Seeed-Studio/OSHW-XIAO-Debug-Mate/1_Libraries/Seeed_Arduino_DAPLink/README.md

# Seeed_Arduino_DAPLink

Most of Seeed & Adafruit boards Seeeduino M0/M4, featuring M0, M4 and nRF52840 are able to run the daplink sketch. It allows us to flash/burn bootloader of any ARM Cortex-M MCU (M0, M4, nRF52832, nRF52840 etc ..) and step debugging with gdb and/or supported IDE such as eclipse,  Keil, IAR. For your convenience, a precompiled daplink firmware in uf2 format for specific board can be found at wiki page

[**More detailed documentation**](https://wiki.seeedstudio.com/Arduino-DAPLink/)

## Contributing
Contributing to this software is warmly welcomed. You can do this basically by<br>
[forking](https://help.github.com/articles/fork-a-repo), committing modifications and then [pulling requests](https://help.github.com/articles/using-pull-requests) (follow the links above<br>
for operating guide). Adding change log and your contact into file header is encouraged.<br>
Thanks for your contribution.
