Seeed-Studio/OSHW-XIAO-Debug-Mate/1_Libraries/lvgl_debug_mate/tests/ref_imgs/draw/render/al88/demo_render_image_recolor_1_opa_128.png

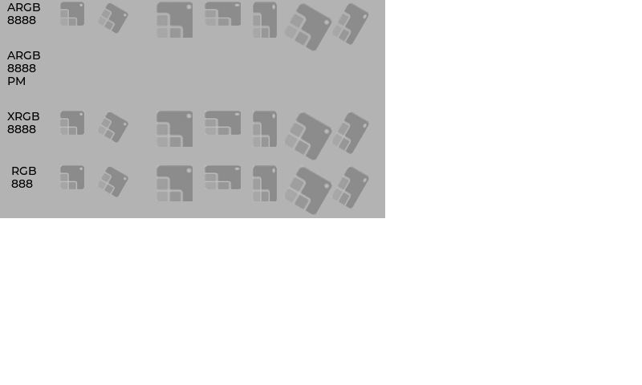
1_Libraries/lvgl_debug_mate/tests/ref_imgs/draw/render/al88/demo_render_image_recolor_1_opa_128.png
