Seeed-Studio/OSHW-XIAO-Debug-Mate/1_Libraries/lvgl_debug_mate/tests/ref_imgs/draw/render/argb8888/demo_render_conical_gradient_opa_255.png

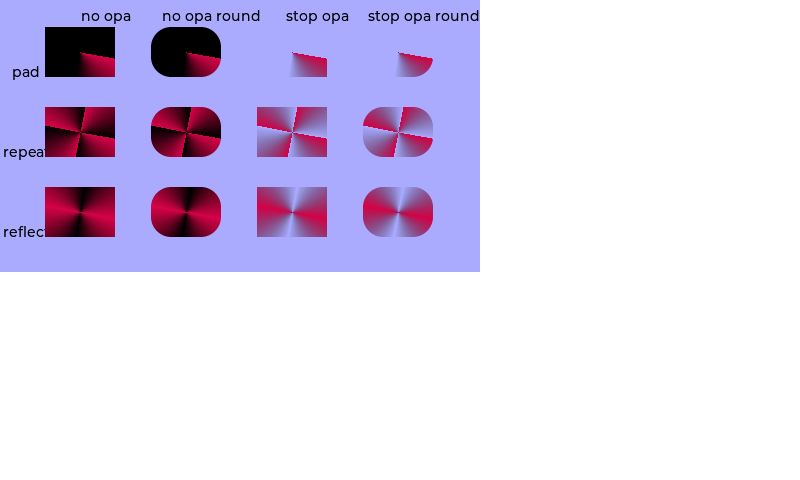
1_Libraries/lvgl_debug_mate/tests/ref_imgs/draw/render/argb8888/demo_render_conical_gradient_opa_255.png
