Seeed-Studio/OSHW-XIAO-Debug-Mate/1_Libraries/lvgl_debug_mate/tests/ref_imgs/draw/render/argb8888_premultiplied/demo_render_blend_mode_opa_255.png

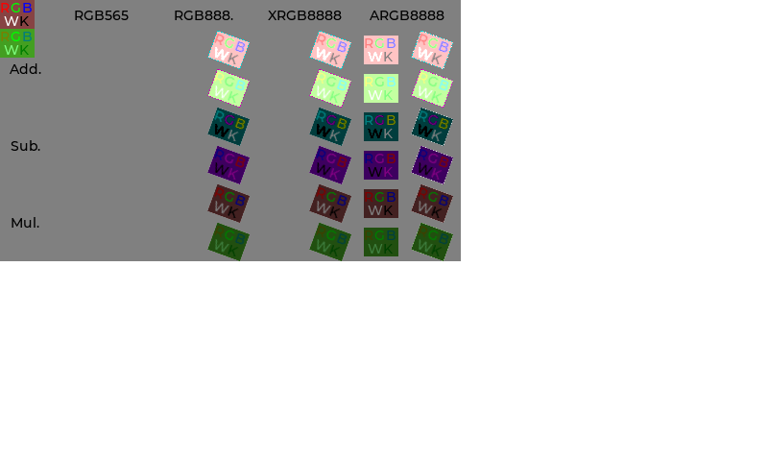
1_Libraries/lvgl_debug_mate/tests/ref_imgs/draw/render/argb8888_premultiplied/demo_render_blend_mode_opa_255.png
