Seeed-Studio/OSHW-XIAO-Debug-Mate/1_Libraries/lvgl_debug_mate/tests/ref_imgs/draw/render/i1/demo_render_box_shadow_opa_255.png

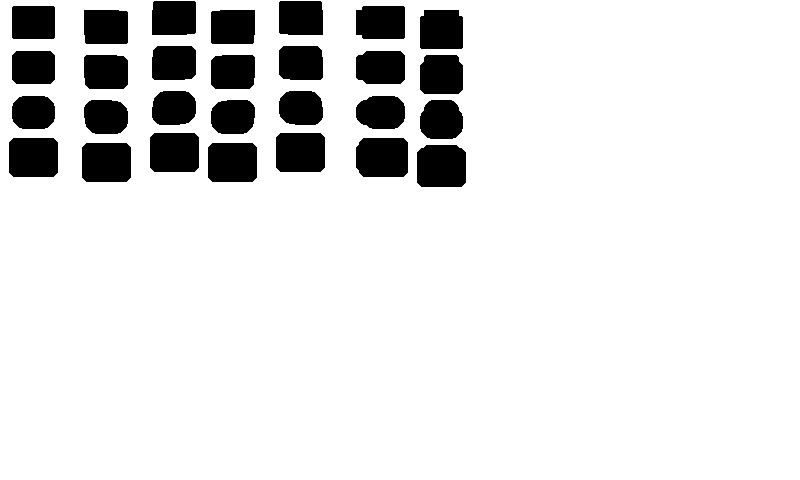
1_Libraries/lvgl_debug_mate/tests/ref_imgs/draw/render/i1/demo_render_box_shadow_opa_255.png
