Seeed-Studio/OSHW-XIAO-Debug-Mate/1_Libraries/lvgl_debug_mate/tests/ref_imgs/draw/render/l8/demo_render_triangle_opa_255.png

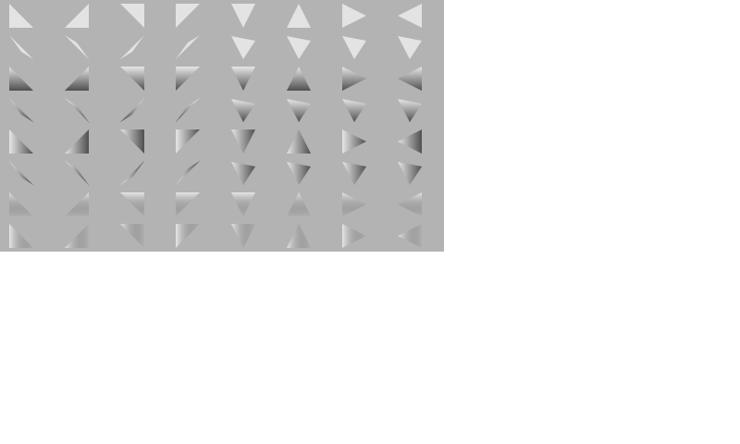
1_Libraries/lvgl_debug_mate/tests/ref_imgs/draw/render/l8/demo_render_triangle_opa_255.png
