Seeed-Studio/OSHW-XIAO-Debug-Mate/1_Libraries/lvgl_debug_mate/tests/ref_imgs_vg_lite/draw/render/argb2222/demo_render_border_opa_255.png

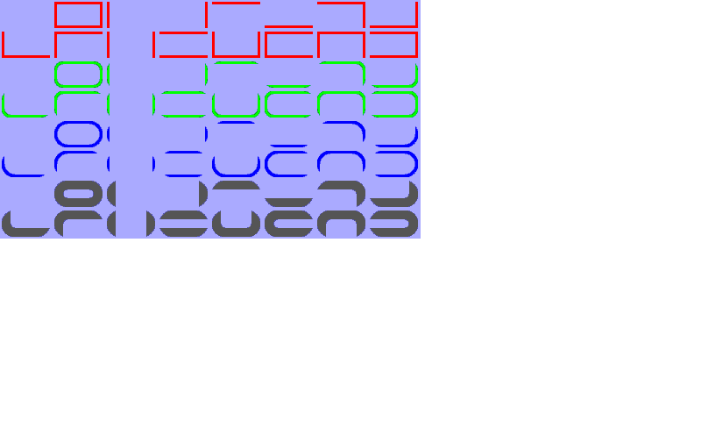
1_Libraries/lvgl_debug_mate/tests/ref_imgs_vg_lite/draw/render/argb2222/demo_render_border_opa_255.png
