Seeed-Studio/OSHW-XIAO-Debug-Mate/1_Libraries/lvgl_debug_mate/tests/ref_imgs_vg_lite/draw/render/argb4444/demo_render_triangle_opa_128.png

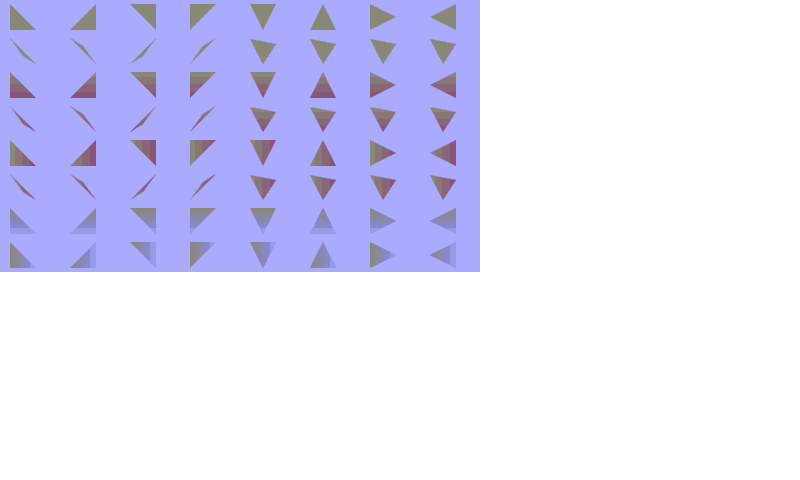
1_Libraries/lvgl_debug_mate/tests/ref_imgs_vg_lite/draw/render/argb4444/demo_render_triangle_opa_128.png
