Seeed-Studio/OSHW-XIAO-Debug-Mate/1_Libraries/lvgl_debug_mate/docs/src/_static/images/home_1.png

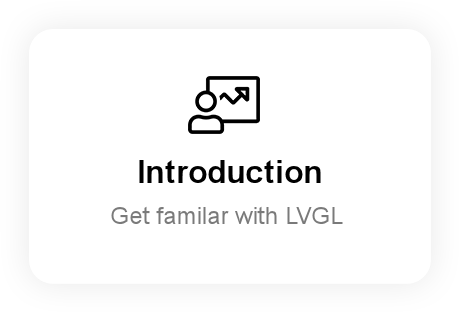
1_Libraries/lvgl_debug_mate/docs/src/_static/images/home_1.png
