Seeed-Studio/OSHW-XIAO-Debug-Mate/1_Libraries/lvgl_debug_mate/docs/src/_static/images/scale_ticks_below.png

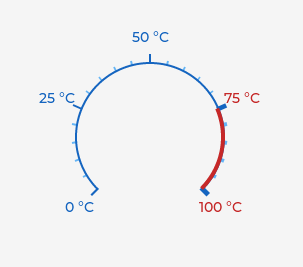
1_Libraries/lvgl_debug_mate/docs/src/_static/images/scale_ticks_below.png
