Seeed-Studio/OSHW-XIAO-Debug-Mate/0_Firmware/src/Global.h

#ifndef GLOBAL_H
#define GLOBAL_H

#define FIRMWARE_VERSION "v1.2"

/* --- Debug switches (uncomment to enable) --- */
// #define POWER_DEBUG

#define BOOT_BTN 0
#define ENCODER_PINA 18
#define ENCODER_PINB 17

#define ShowSerial  Serial
#define COMSerial   Serial0
#define UART_SWITCH 48

#define LED_DATA    9
#define LED_CLOCK   7
#define LED_LATCH   8

#define MOS1_PIN     16
#define MOS2_PIN     15
#define INA_I2C_SDA  4
#define INA_I2C_SCL  3
#define INA_I2C_ADDR 0x43
#define INA_I2C_FREQUENCY 100000

#define EEPROM_I2C_SDA 1
#define EEPROM_I2C_SCL 2
#define EEPROM_I2C_ADDR 0x50
#define EEPROM_I2C_FREQUENCY 100000

/*Set to your screen resolution and rotation*/
#define TFT_HOR_RES   240
#define TFT_VER_RES   320
#define TFT_ROTATION  LV_DISPLAY_ROTATION_90

#define DEBOUNCE_DELAT 50       // Debounce delay, in milliseconds
#define LONG_PRESS_DELAY 1000   // Long press delay, in milliseconds

#define DELETE_LABEL(label)   \
if (label != nullptr) {   \
lv_obj_del(label);     \
label = nullptr;       \
}

extern unsigned long startTime;
extern bool daplinkStatus;

#endif
